fthiebolt/neOCampus-arduino/pcb/old-altium-pcb-v3/single-ic-preamp-by-lm358.pdf

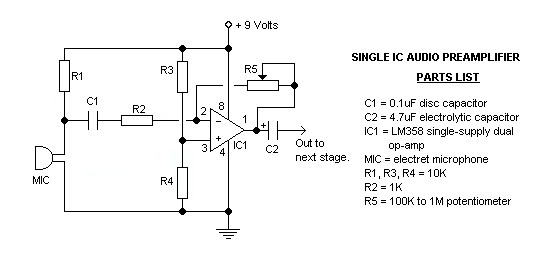
[picture p2: page 1]
