fthiebolt/neOCampus-arduino/pcb/old-altium-pcb-v3/sonometre2.pdf

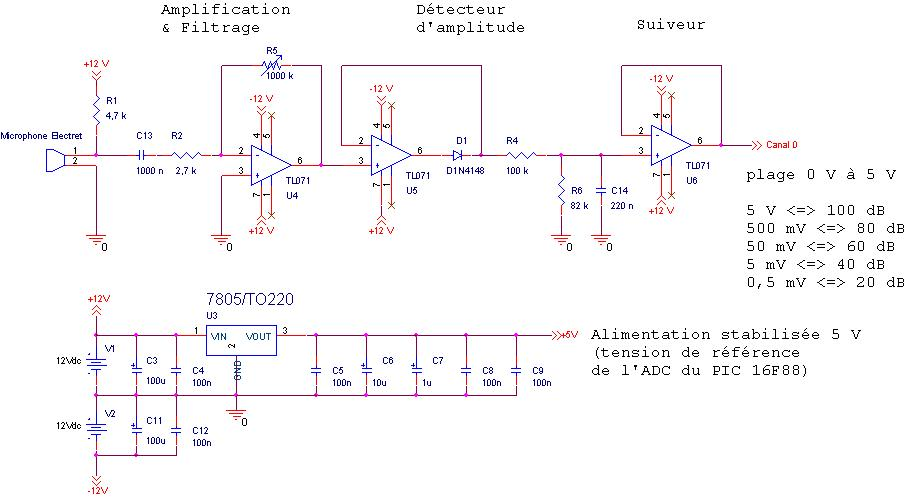
[picture p3: page 1]
