fthiebolt/neOCampus-arduino/pcb/old-altium-pcb-v3/TaaraESP-SHT21.sch_.pdf

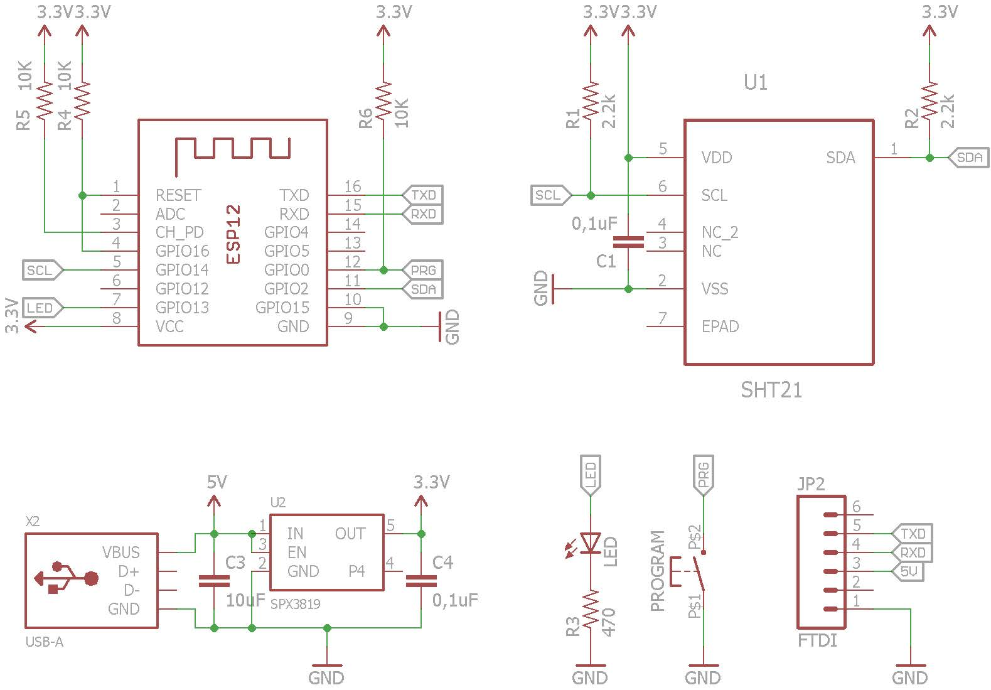
[picture p4: page 1]
