fthiebolt/neOCampus-arduino/lasercut/LaserCut-parameters_oct23.jpg

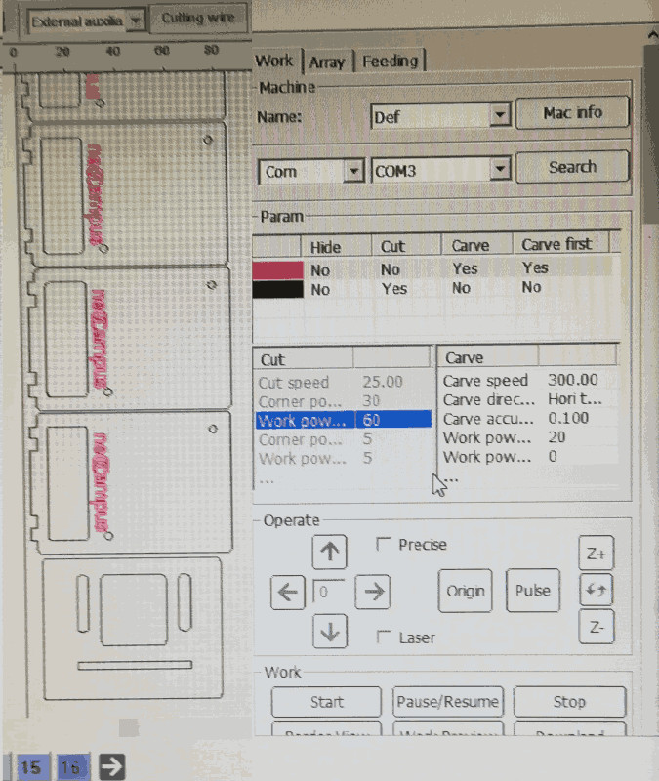
lasercut/LaserCut-parameters_oct23.jpg
