fthiebolt/neOCampus-arduino/pcb/pcb-v5/layout-outline.pdf

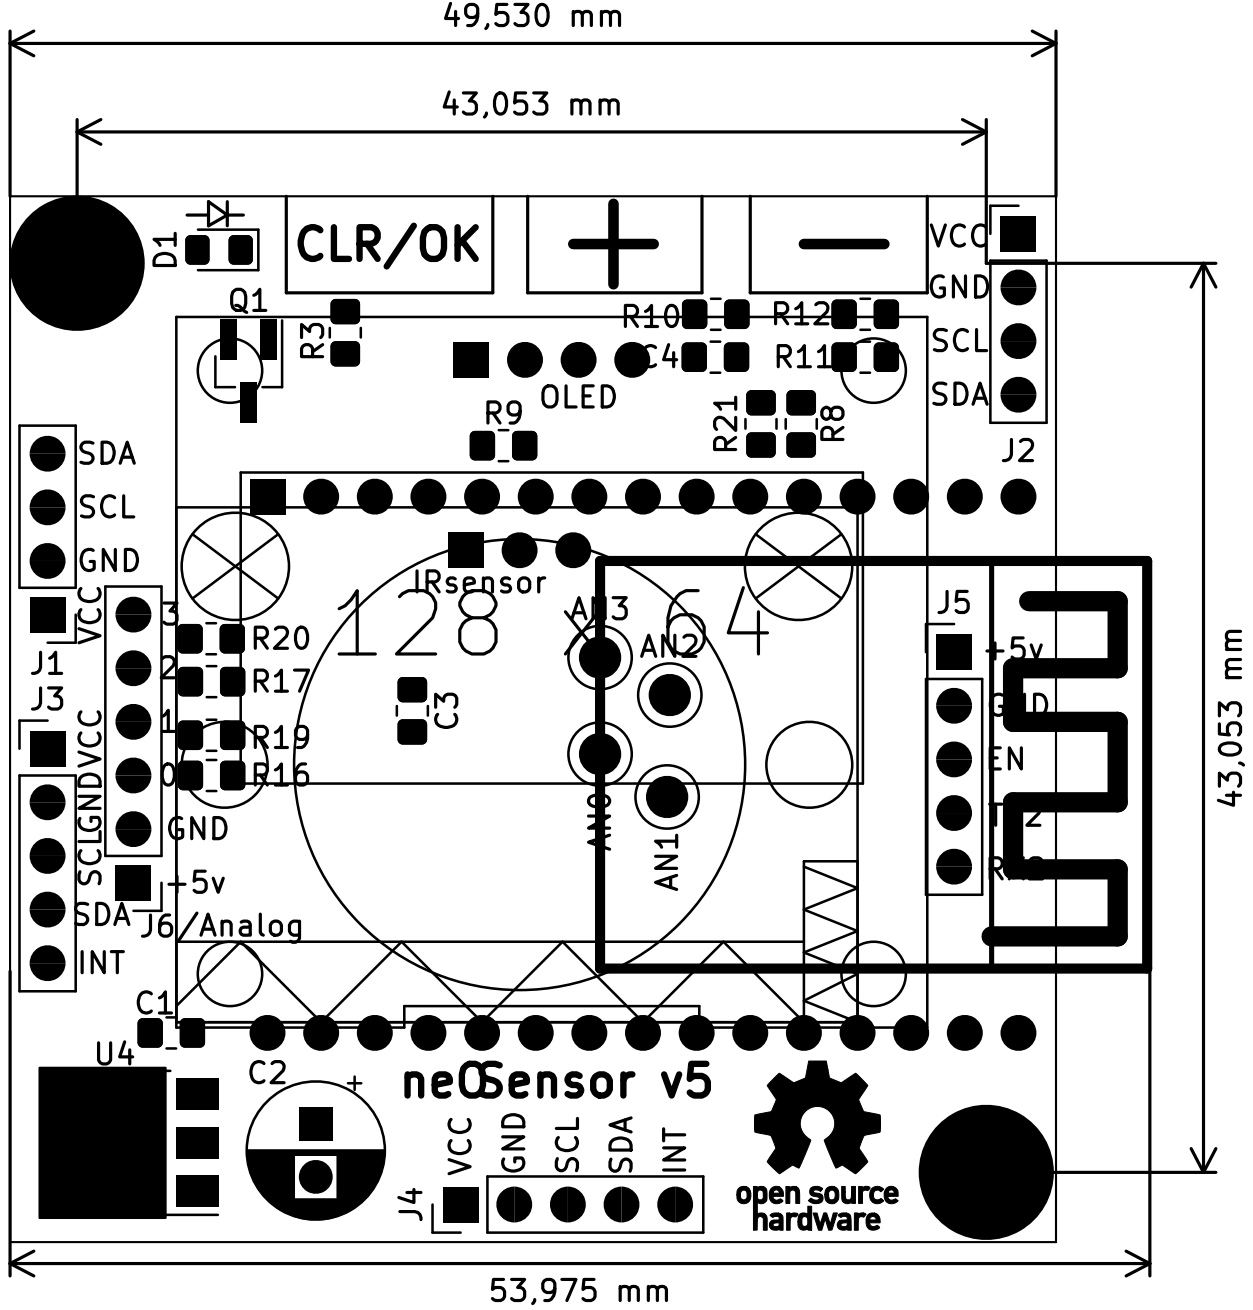
[picture p32: page 1]
