fthiebolt/neOCampus-arduino/pcb/old-altium-pcb-v3/Cpt_temperature.pdf

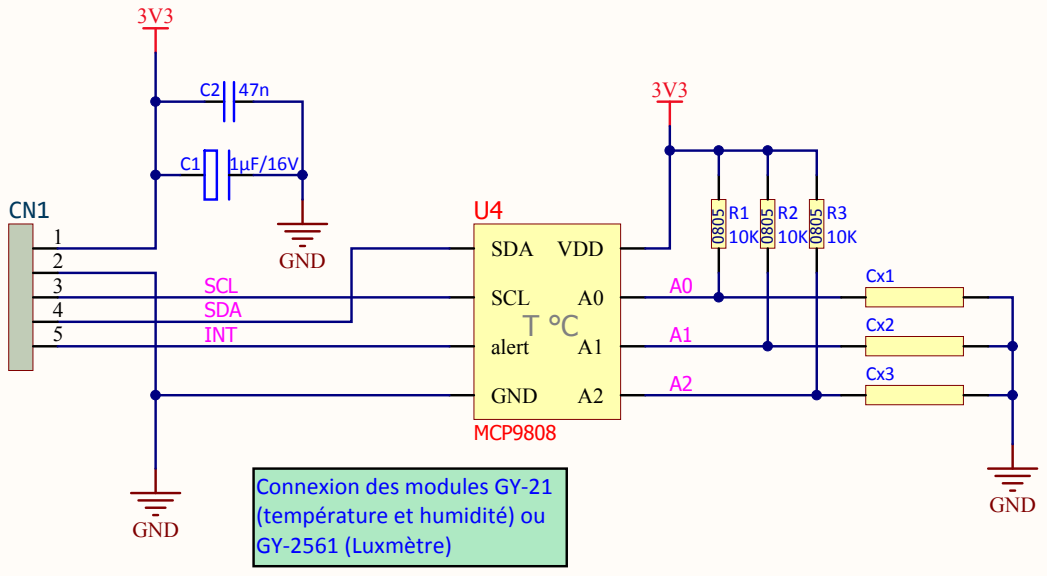
[picture p33: page 1]

GND

SDA | A1
INT

Connexion des modules GY-21
(température et humidité) ou
GY-2561 (Luxmètre)

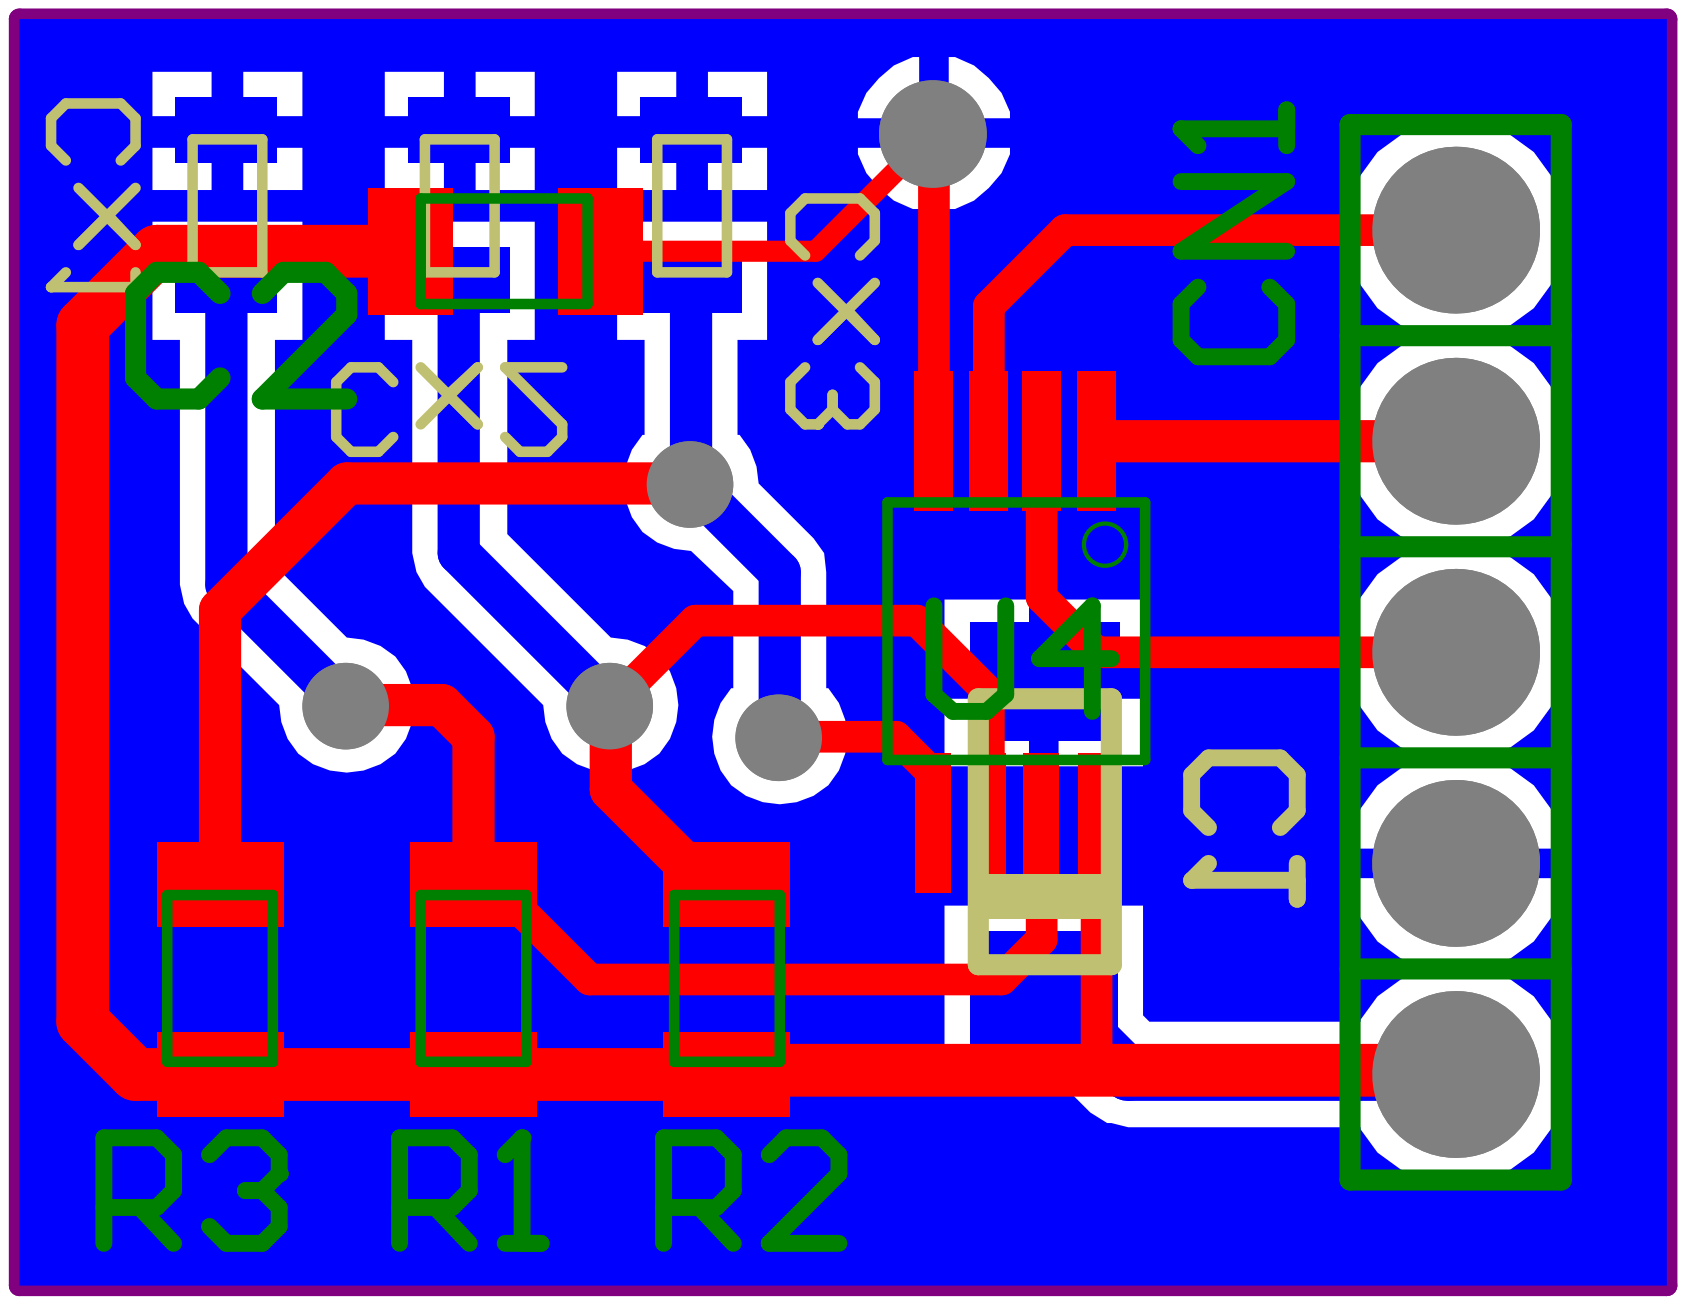
[picture p34: page 2]

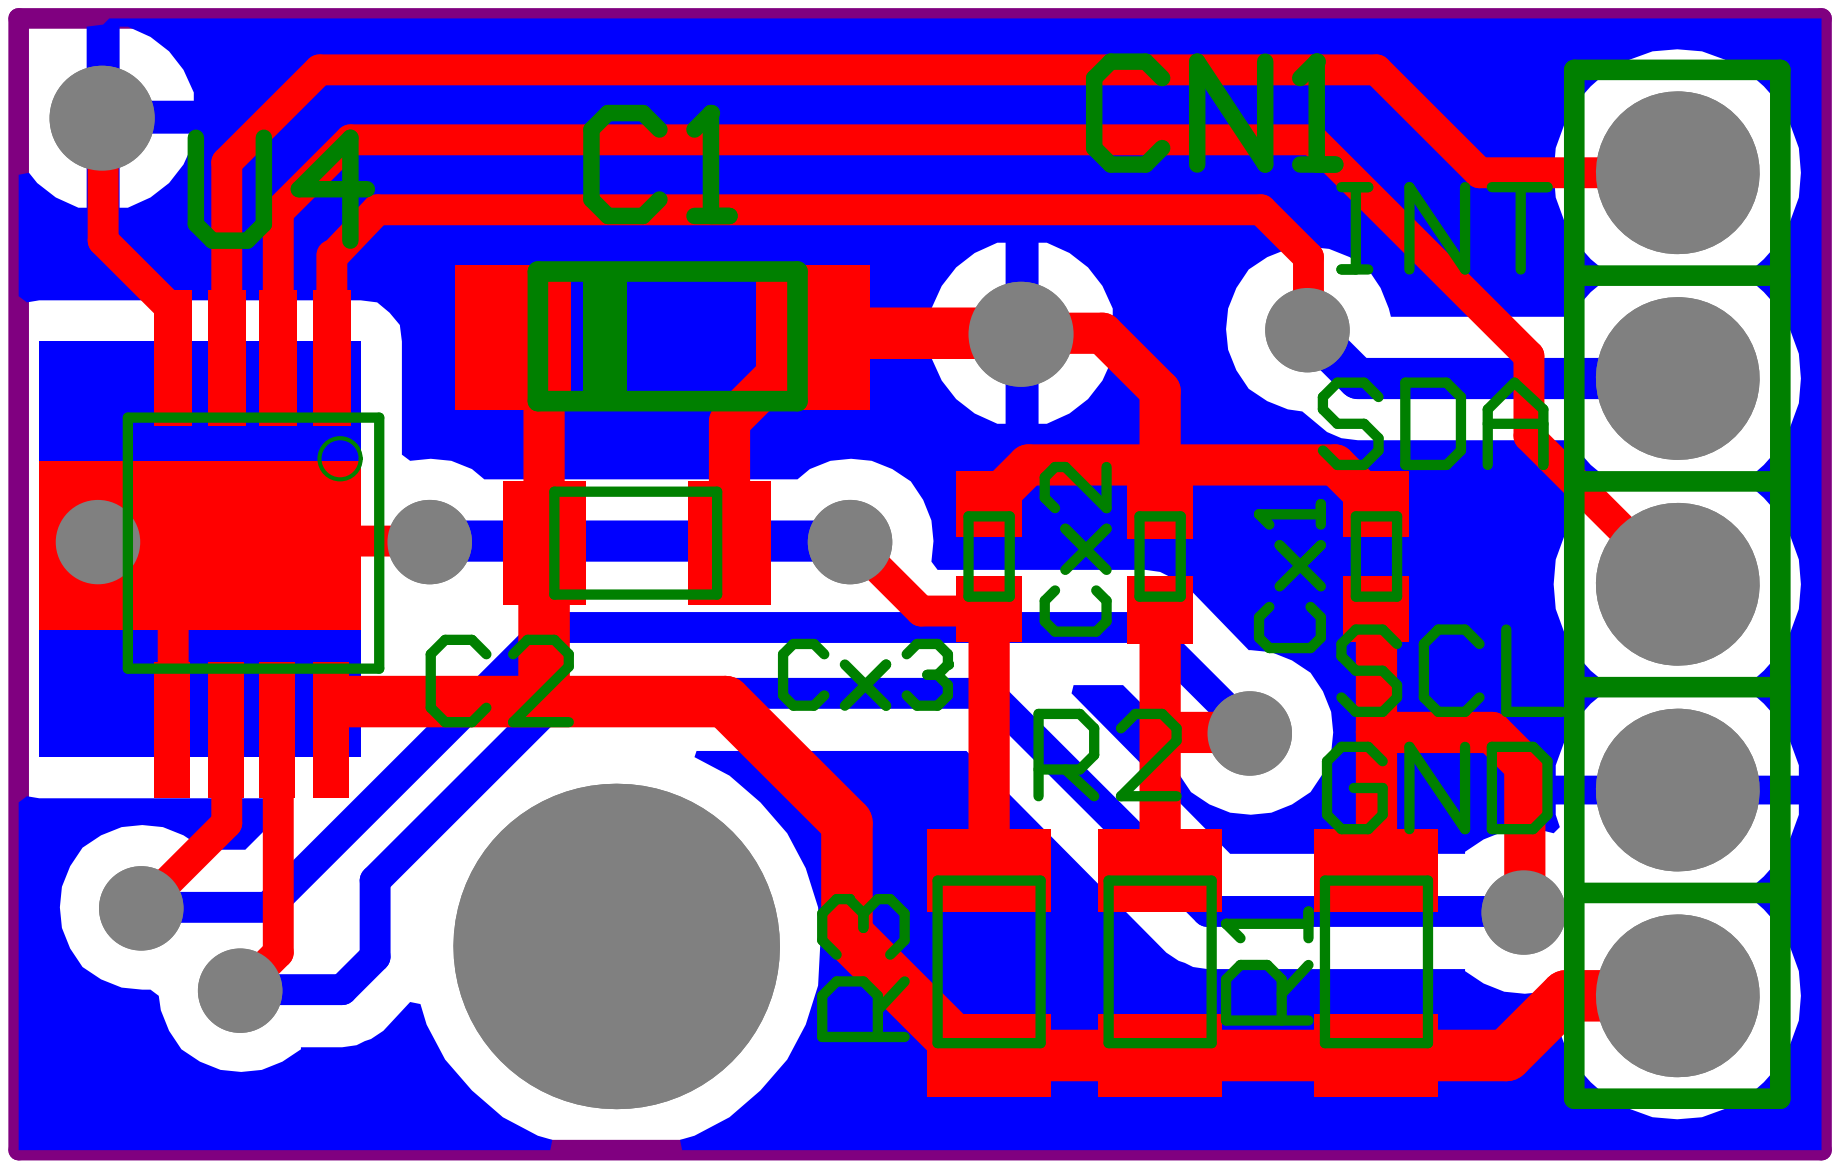
[picture p35: page 3]

Comment | Description | Designator | Footprint | LibRef | Quantity
1µF/ 16V | 145-7406 case 3216-18 | C1 | 3216-18 | tantale 1µF/ 16V | 1
47n | CMS 0805 | C2 | 0805 | Cap_CMS_0805 | 1
inch_ligne 1x5 | Inch_1x5_droit | CN1 | INCH_1x5_droit | Inch_1x5_droit | 1
Pont | Pont pour configuration I2C | Cx1, Cx2, Cx3 | 0402 | Pont | 3
10K | CMS 0805 | R1, R2, R3 | 0805 | Res CMS 0805 | 3
MCP9808 | Digital temperature SeU4 | | MSOP-08 | MCP9808 | 1
