fthiebolt/neOCampus-arduino/pcb/old-altium-pcb-v3/Son_BU.pdf

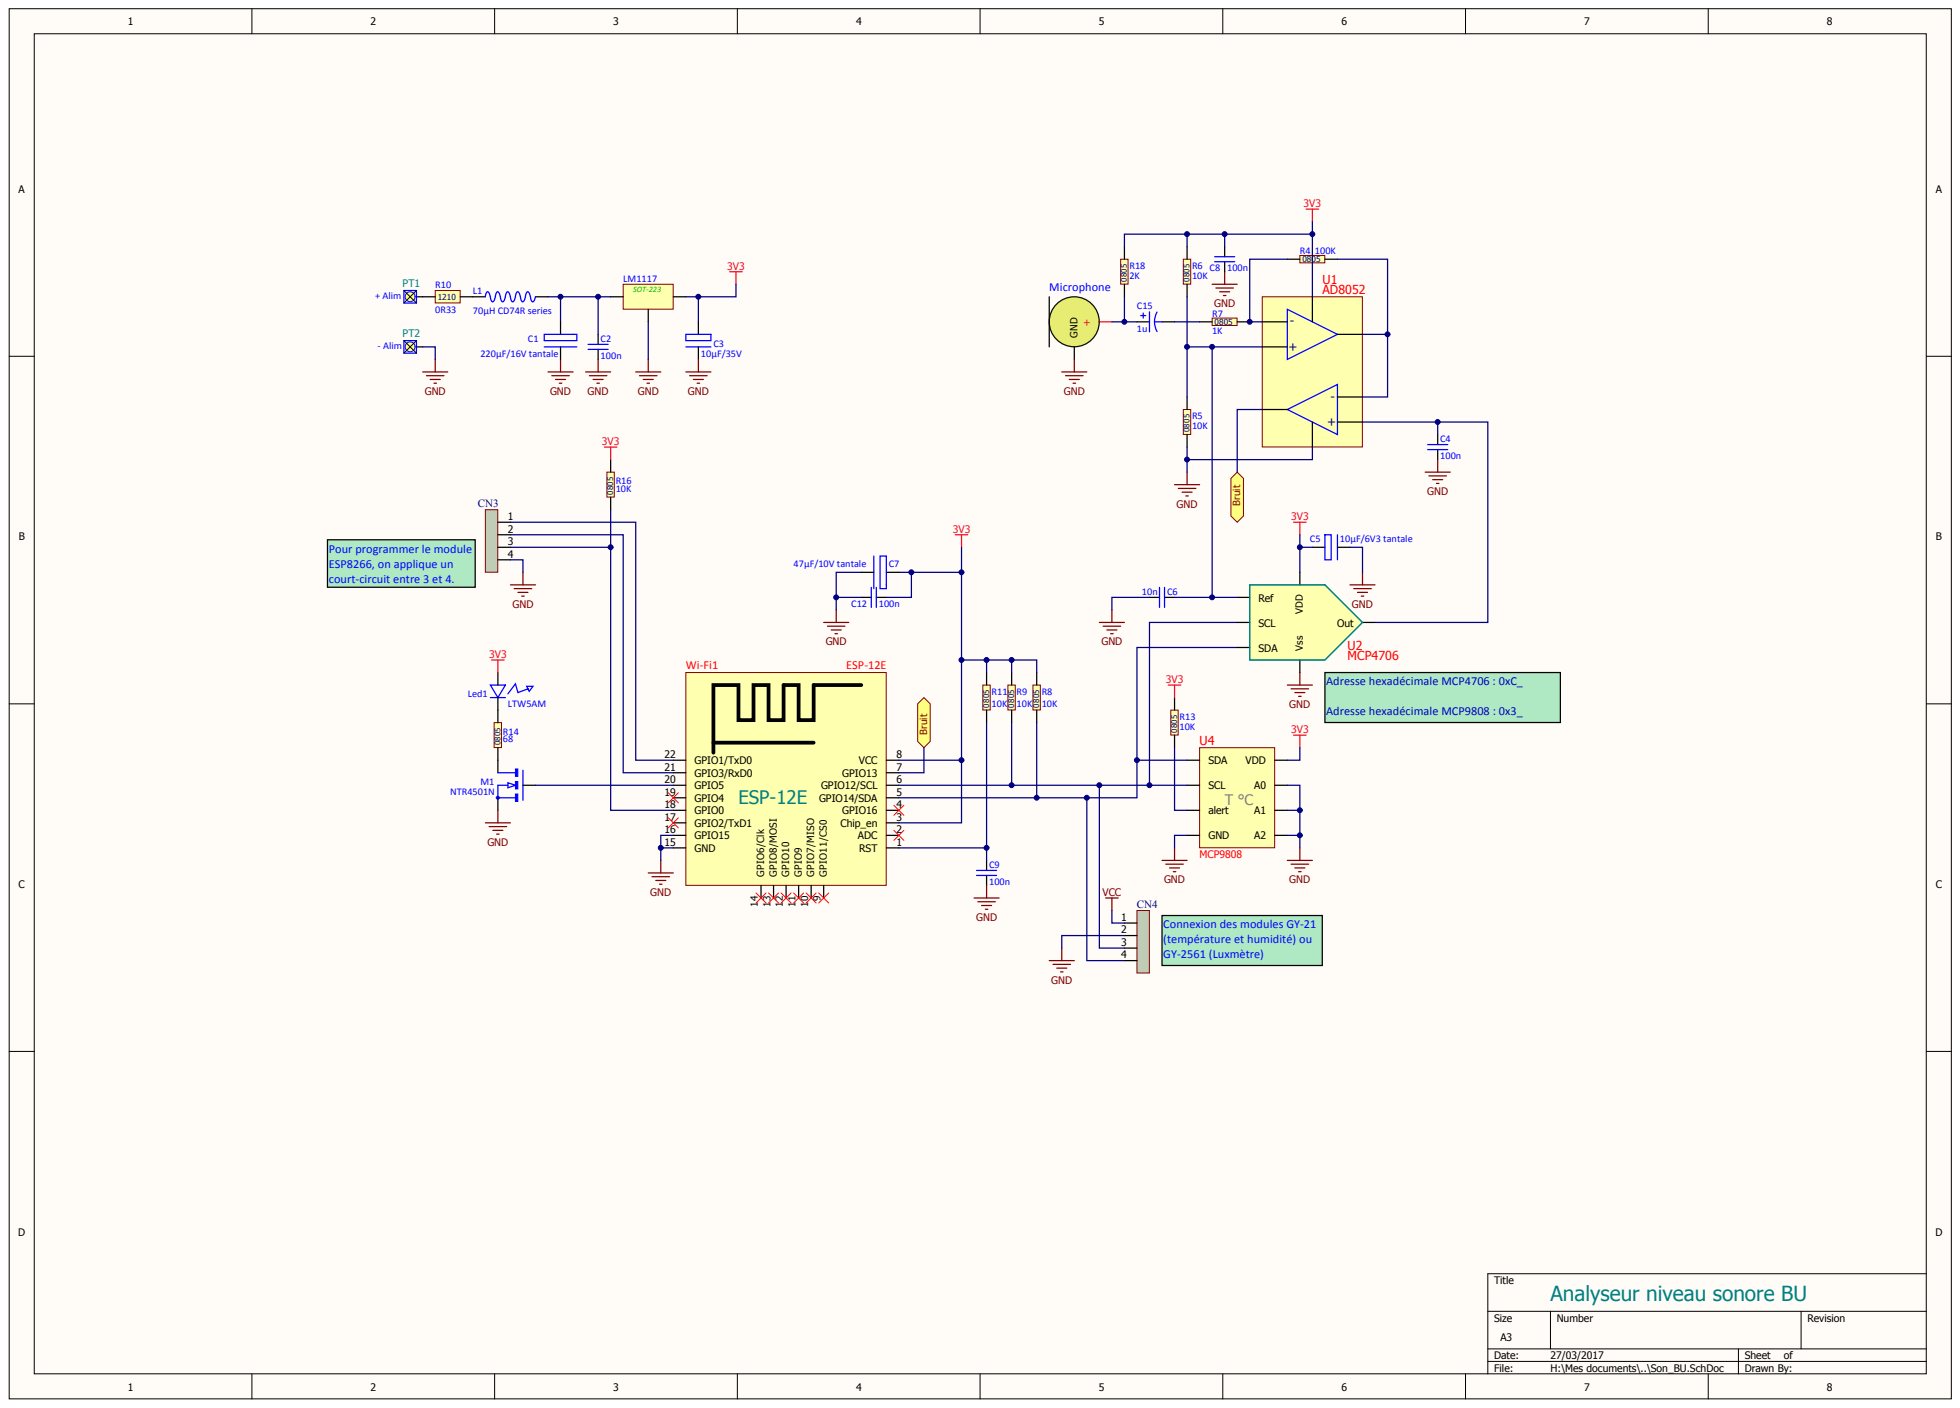
[picture p36: page 1]

Pour programmer le module
ESP8266, on applique un
court-circuit entre 3 et 4.

Connexion des modules GY-21
(température et humidité) ou
GY-2561 (Luxmètre)

Titl
Analyseur niveau sonore BU

Bill of Materials | <Parameter Title not found>
Source Data From: | Son_BU.PrjPCB
Project: | | Son_BU.PrjPCB
Variant: | | None
Creation Date: 27/03/2017 | 09:28:08
Print Date: | 42821 | 42821,39458
Footprint | Comment | LibRef | Designator | Description | Quantity
7343-31 | 220µF/16V
| tantale | tantale
| | 220µF/16V | C1 | 253-5290 | 1
0805 | 100n | Cap_CMS_0805 | C2, C4, C8, C9, C12 | CMS 0805 | 5
Condo CMS POL diam.5 | 10µF/35V | 10µF/35V | C3 | électrochimique CMS 185-0112 | 1
Tantale 10µF/6V3 | 10µF/6V3
| tantale | tantale
| | 10µF/6V3 | C5 | 175-4041 ou 145-7412 case 3216-18 | 1
0805 | 10n | Cap_CMS_0805 | C6 | CMS 0805 | 1
tantale 47µF/10V | 47µF/10V
| tantale | tantale
| | 47µF/10V | C7 | 175-4168 | 1
RB7.6-15 | Cap Pol1 | Cap Pol1 | C15 | Polarized Capacitor (Radial) | 1
INCH_1x4_dr oit | inch_ligne 1x4 | Inch_1x4_droit | CN3, CN4 | Inch_1x4_droit | 2
SELF CD74R | 70µH CD74R
| series | Self CD74R | L1 | SMT CD74R Aliexpress | 1
LTW5AM | LTW5AM | LTW5AM LED | Led1 | LED Golden Dragon Plus | 1
SOT-223 thermo1 | LM1117/33 | LM1117MPX-3.3 | LM1117 | Régulateur SOT-223 | 1
SOT23 (NTR4501) | NTR4501N | NTR4501N | M1 | MOSFET canal N | 1
Micro_electre t | Microphone_01 | Microphone_01 | Microphone | | 1
Pointe de test | + Alim | PTEST | PT1 | pointe de test CI 133-6225 | 1
Pointe de test | - Alim | PTEST | PT2 | pointe de test CI 133-6225 | 1
0805 | 100K | Res CMS 0805 | R4 | CMS 0805 | 1
0805 | 10K | Res CMS 0805 | R5, R6, R8, R9, R11, R13, R16 | CMS 0805 | 7
0805 | 1K | Res CMS 0805 | R7 | CMS 0805 | 1
1210 | 0R33 | Res CMS 1210
| | ERJ14B | R10 | CMS 1210 | 1
0805 | 68 | Res CMS 0805 | R14 | CMS 0805 | 1
0805 | 2K | Res CMS 0805 | R18 | CMS 0805 | 1
SOIC08 | AD8052 | AD8052 | U1 | AOP | 1
SOT23-6 | MCP4706 | MCP4706_1 | U2 | DAC I2C (RS : 738-7111) | 1
MSOP-08 | MCP9808 | MCP9808 | U4 | Digital temperature Sensor | 1
ESP-12E | ESP-12E | ESP-12E | Wi-Fi1 | ESP-12E module Wi-Fi | 1
| | | | | 36
Approved | | Notes
