fthiebolt/neOCampus-arduino/pcb/old-altium-pcb-v3/Assembly Drawings.pdf

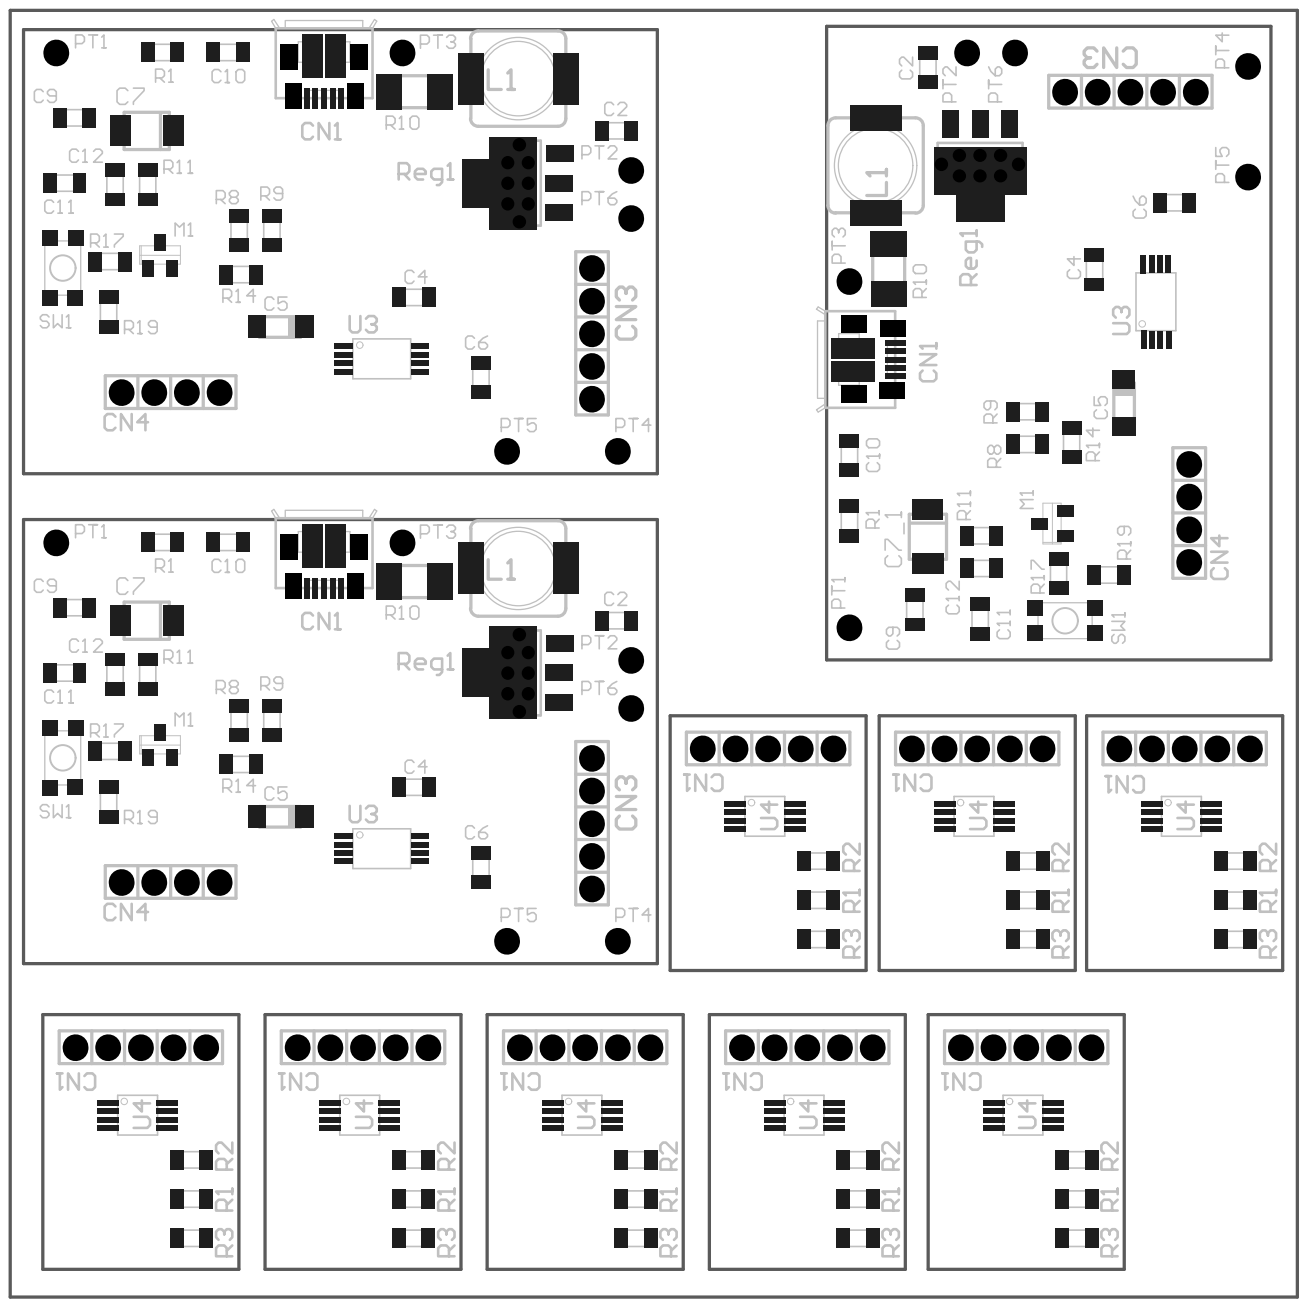
[picture p44: page 1]

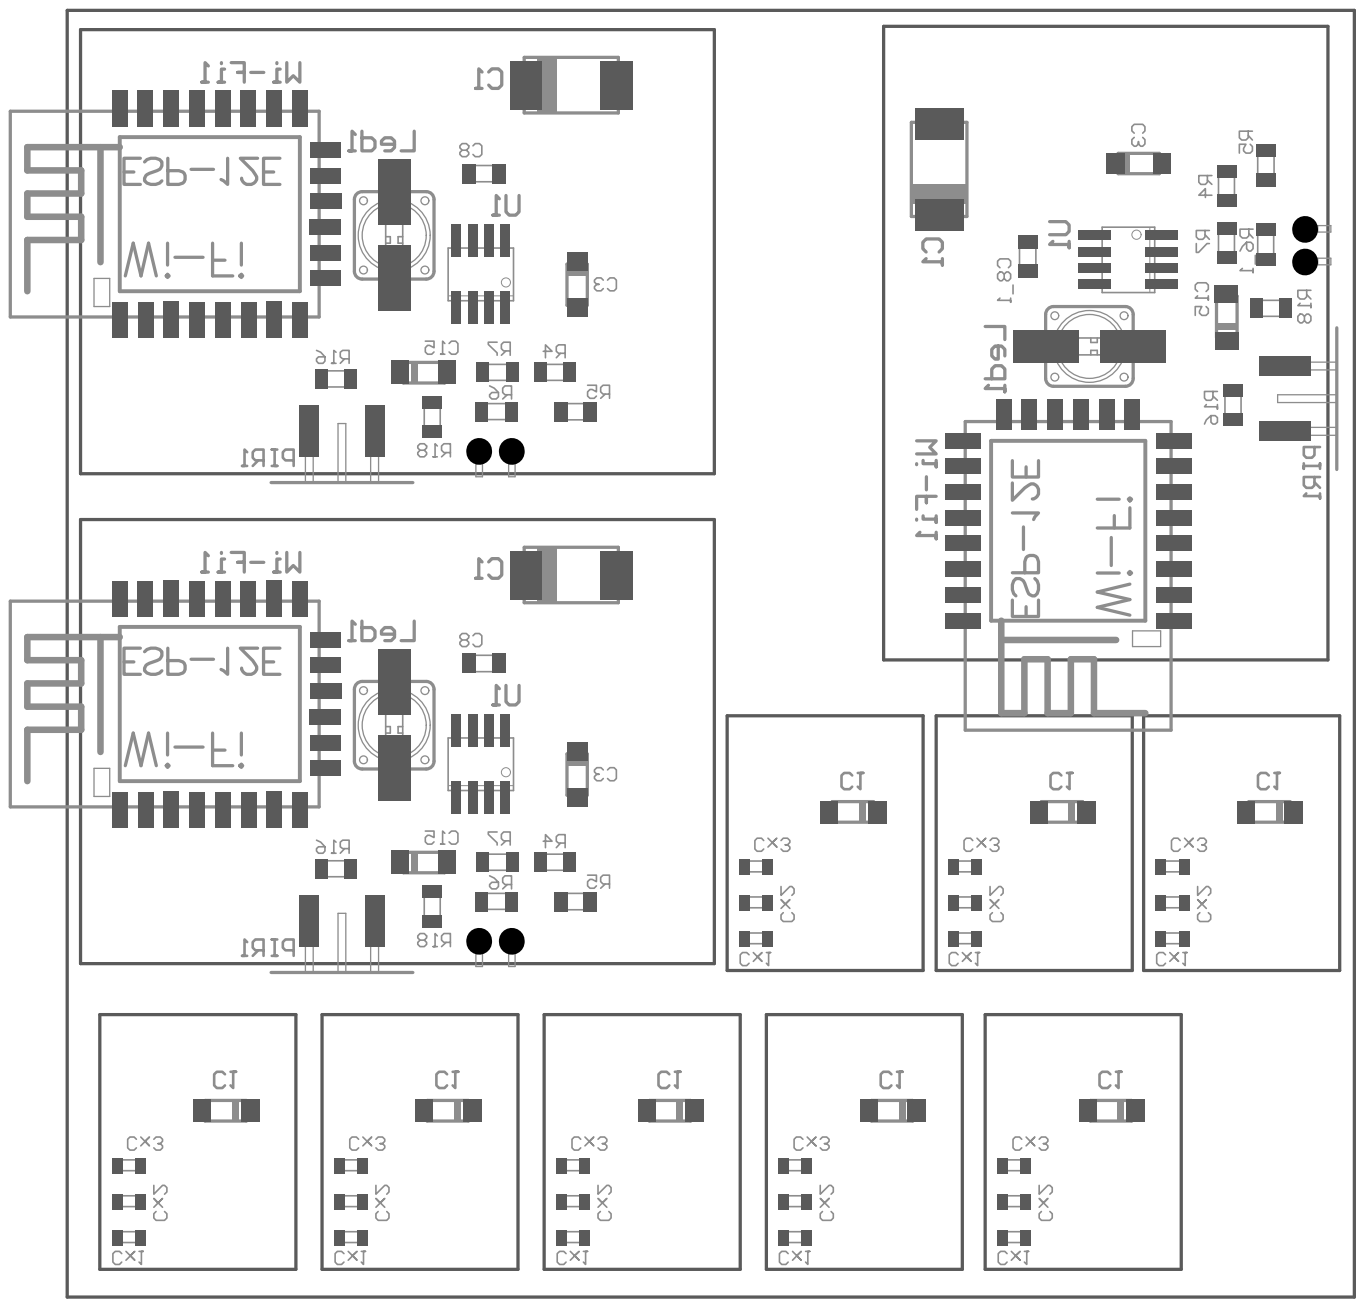
[picture p45: page 2]
