fthiebolt/neOCampus-arduino/pcb/pcb-v4/neOSensor-v4-schematic.pdf

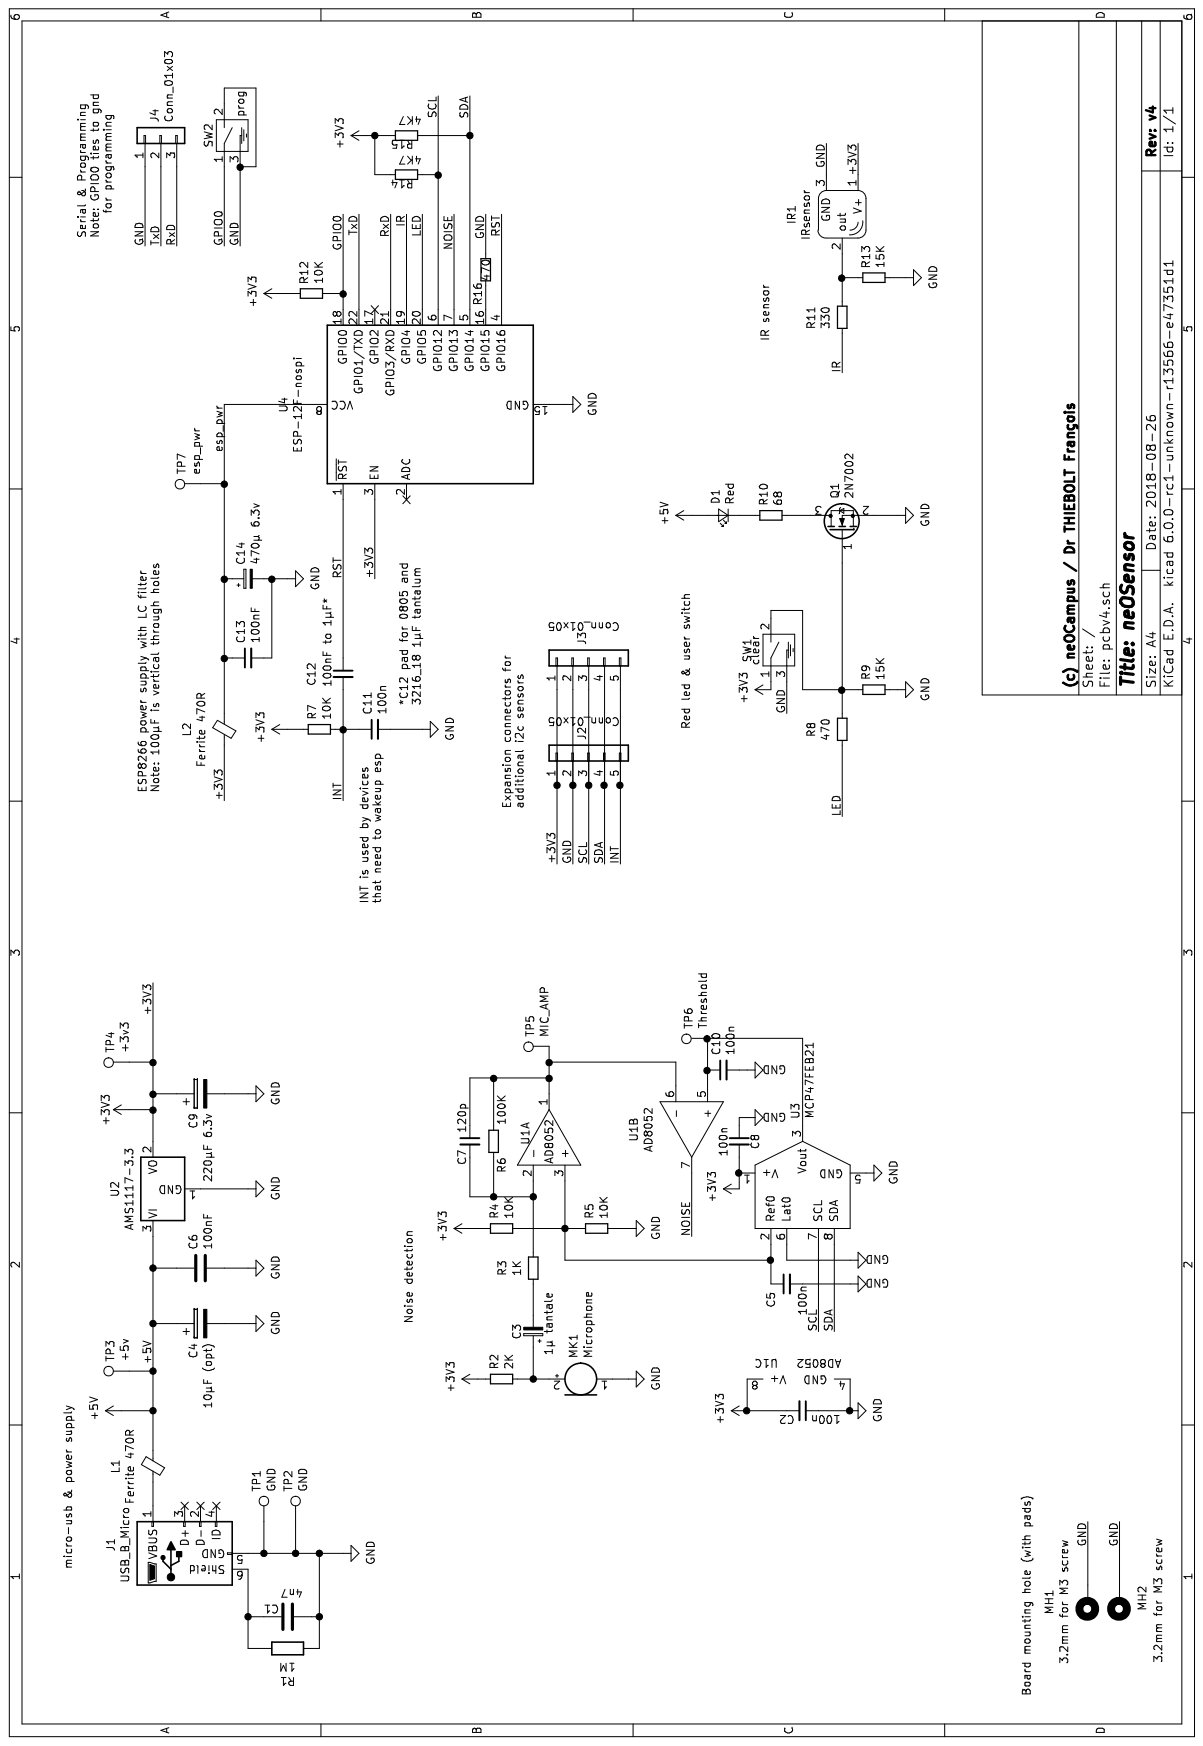
[picture p46: page 1]
