fthiebolt/neOCampus-arduino/pcb/old-altium-pcb-v3/Composite Drill Drawing.pdf

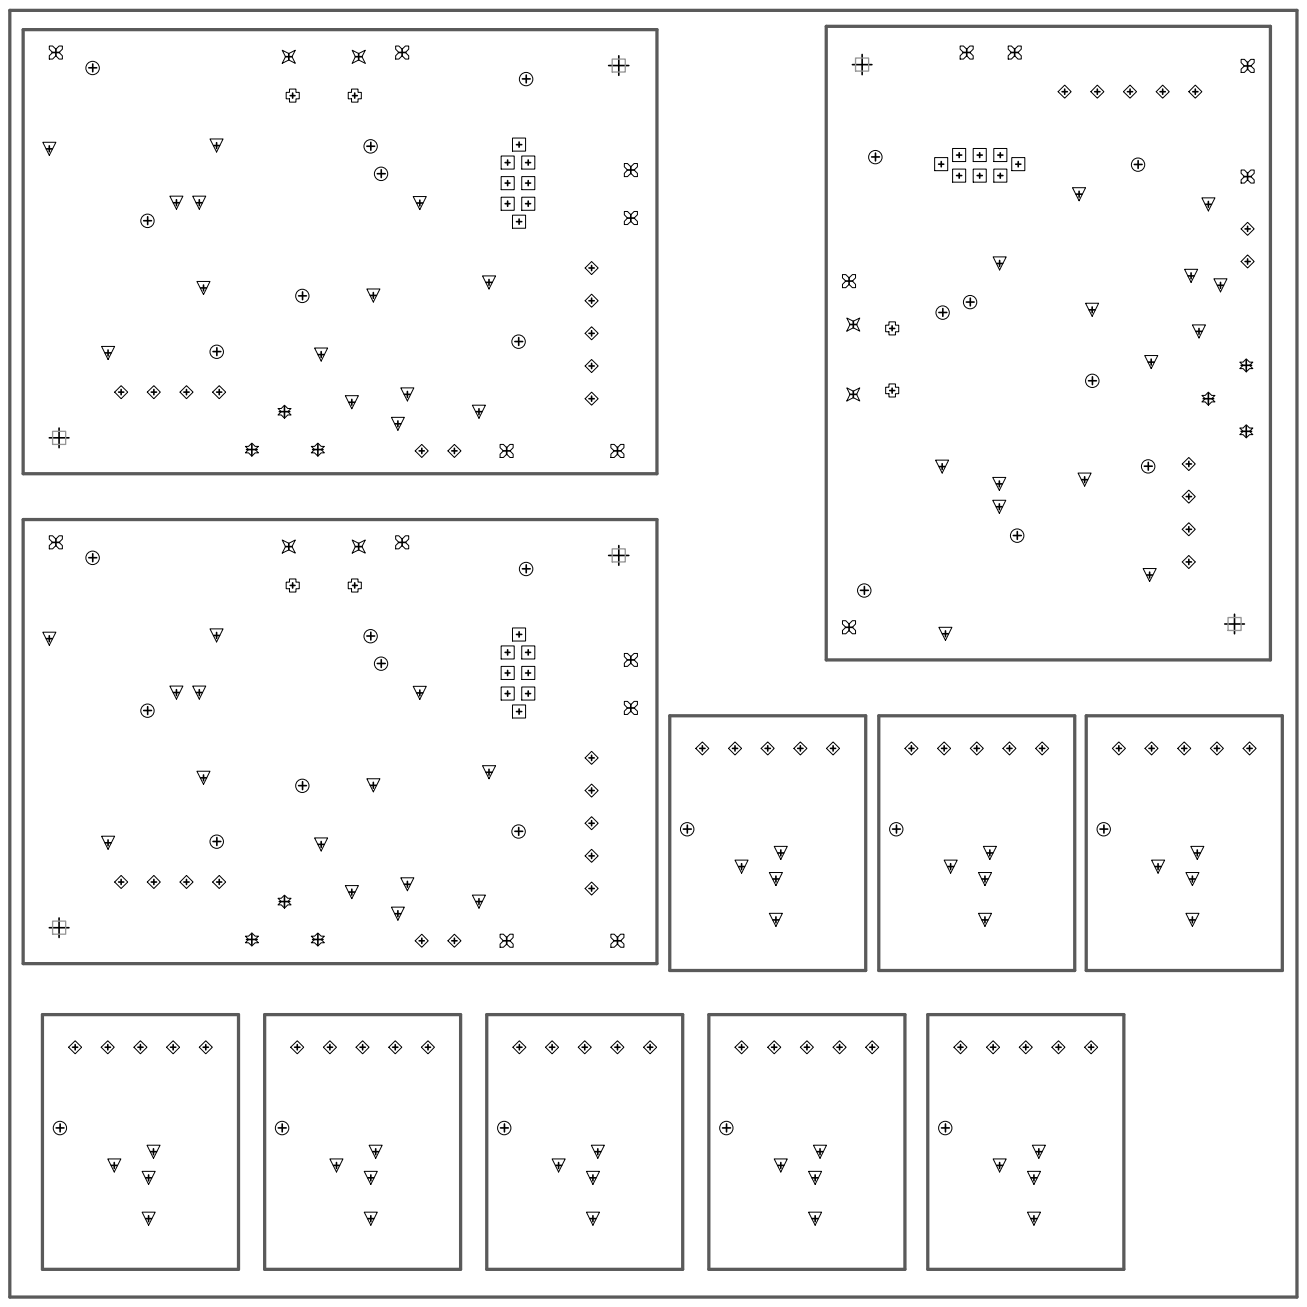
[picture p47: page 1]
