fthiebolt/neOCampus-arduino/pcb/pcb-v4/pcbv4-drilling4faces.pdf

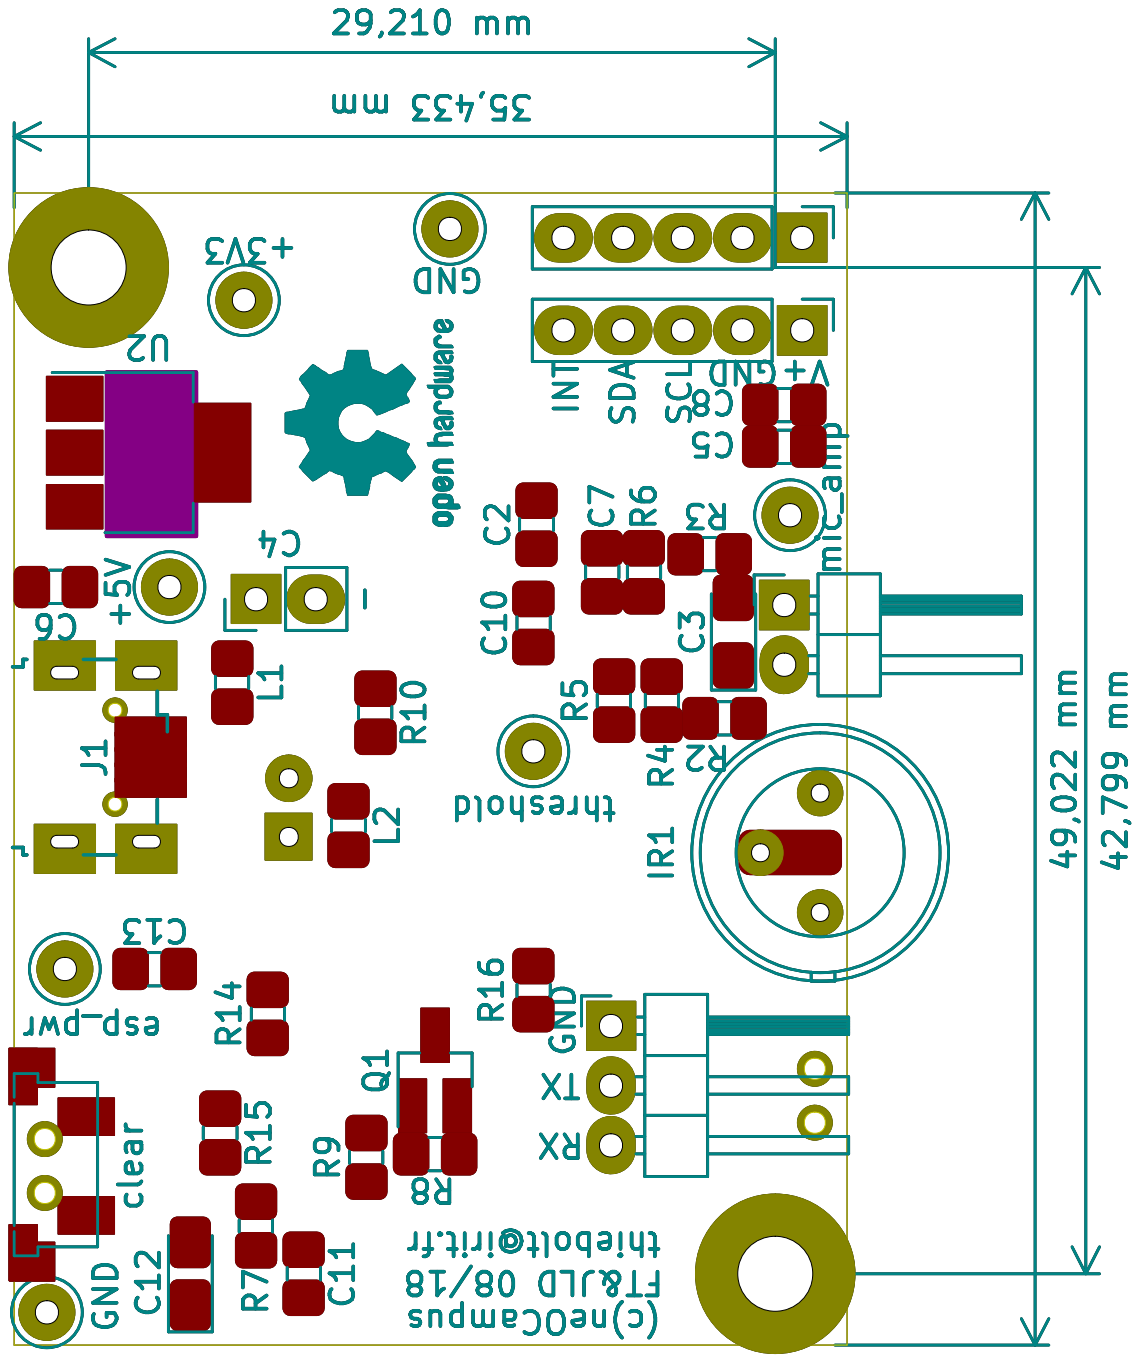
[picture p48: page 1]
