fthiebolt/neOCampus-arduino/src/neosensor/src/httpsclient.cpp

#include "httpsclient.hpp"

httpsclient::httpsclient () {};

StaticJsonDocument<CRED_JSON_SIZE> httpsclient::get_credentials(uint8_t *mac_addr){
    /* TODO 
     * Add certificate if unsecure connection successful
     */
    log_debug("--- beg of httpsclient::get_credentials ---");
    const char* root_ca = NULL;
    const char* _cacert = NULL;
    const char* _clicert = nullptr;
    const char* _clikey = nullptr;
    StaticJsonDocument<CRED_JSON_SIZE> cred_json;
    WiFiClientSecure *wcsClient = new WiFiClientSecure;
    wcsClient->setCACert(_cacert);
    wcsClient->setCertificate(_clicert);
    wcsClient->setPrivateKey(_clikey);

    snprintf(_url, sizeof(_url), "%s%s%02X:%02X:%02X:%02X:%02X:%02X", AUTH_SERVER, CRED_REQ, mac_addr[0],mac_addr[1],mac_addr[2],mac_addr[3],mac_addr[4],mac_addr[5]);
    //log_debug(_url);
    if(!_https.begin(*wcsClient, _url)){
        log_error("Beginning of https communication failed" );
    }else{
        log_debug("https communication established");
        int httpCode= _https.GET(); 
        log_debug(httpCode);
        String payload;
        if (httpCode > 0) { 
            //Check for the returning code
            payload = _https.getString();
        }
        /* Unboxing credentials from cred server */
        DeserializationError error = deserializeJson(cred_json, payload);
        Serial.println("Credentials requested from auth");
        log_debug(_url);
        _https.end();   
        // Test if parsing succeeds.
        if (error) {
            Serial.print(F("deserializeJson() failed: "));
            Serial.println(error.c_str());
        }else{
            log_debug("--- end of httpsclient::get_credentials ---");
        }
    }
    return cred_json;
}
