fthiebolt/neOCampus-arduino/src/neosensor/src/esp32_memory.hpp

#ifndef MEMORY_HPP
#define MEMORY_HPP

#include <Arduino.h>
#include <ArduinoJson.h>
#include <FS.h>
#include <LITTLEFS.h>
#include "const.hpp"
#include "neologger.hpp"

class esp32_memory{
public:
    /* starting the file system*/
    esp32_memory();
    bool begin(bool);


    void makedir(const char * path);

    void rmvdir(const char * path);

    /* checks if a file exists */
    bool exists(const char *);

    /* Writes a buffer int a file */
    void write(const char *, StaticJsonDocument<MAX_JSON_SIZE>);
    /* Read from a file
     * return what has been read.
     */
    StaticJsonDocument<MAX_JSON_SIZE> read(const char *);
};



#endif
