fthiebolt/neOCampus-arduino/src/neosensor/src/mqttsclient.hpp

#ifndef MQTTSCLIENT_HPP
#define MQTTSCLIENT_HPP

#include <Arduino.h>
#include <PubSubClient.h>
#include <WiFiClientSecure.h>
#include "const.hpp"
#include "neologger.hpp"


class mqttsclient{
public:
    /* Default constructor leads to the sandbox mode */
    mqttsclient(const char *login = DEFT_LOGIN, const char *pwd = DEFT_PWD, const char *server = DEFT_SERVER, unsigned int port = DEFT_PORT,const char *topic_base = DEFT_TOPIC_BASE, const char *topic = DEFT_TOPIC);
    /* destructor */
    ~mqttsclient();
    /* callback renamed to fit neOCampus logic */
    void on_message(char* topic, byte *payload, unsigned int length); //TODO
    /* subscribe to topic */
    bool subscribe(); //TODO
    /* publish */
    bool publish(); //TODO
    /* add a sensor class to the sensitivity list*/
    bool add(const char *, void(*)(byte *, unsigned int)); //TODO
    /* connection to the MQTT broker*/
    bool connect();
    /* reconnect if connection lost */
    void reconnect();
    /* print attributes to serial */
    void serialize();

    /* extracts the topic from the long string returned by the callback*/ 
    char * split_topic(char *topic_chain);
private:
    WiFiClientSecure *_wcsClient = new WiFiClientSecure;
    PubSubClient _client; 
    const char *_login; 
    const char *_pwd; 
    const char *_server;
    const char *_topic_base;
    const char *_topic;
    const unsigned int _port;
    struct users{
        const char* topic;
        size_t topic_size;
        void(*on_message)(byte*, unsigned int);
    } _users [MAX_SENSORS]; 
    int _numb_users;


};


#endif
