fthiebolt/neOCampus-arduino/tests/dual_MQTTS_subscription_test/dual_MQTTS_subscription_test.ino

#include <WiFiManager.h>
#include <HTTPClient.h>
#include <PubSubClient.h>
#include <ArduinoJson.h>
#include <SPIFFS.h>

#define CREDENTIALS "/cred.txt"
#define CONFIG "/conf.txt"

#define DEFT_LOGIN "test"
#define DEFT_PWD "test"
#define DEFT_SERVER "neocampus.univ-tlse3.fr"
#define DEFT_TOPIC "TestTopic/airquality"
#define DEFT_TOPIC_CLASS "TestTopic/airquality/command"
#define DEFT_SEC_TOPIC "TestTopic/temperature"
#define DEFT_SEC_TOPIC_CLASS "TestTopic/temperature/command"

#define DEFT_PORT 8883

/* MAC vars */
uint8_t macAddr[6];
char strMacAddr[32];

/*WiFiManager vars */
char ssid[20]; /*WM ssid defined by device's class + part of MAC address*/
const char* pwd = "password"; /* need 8 char pwd else autoConnect fails.*/
WiFiManager wm;

/*HTTPS vars*/
HTTPClient httpsClient;
const char* root_ca = NULL;
char url [90];
const char* config_server = "https://sensocampus.univ-tlse3.fr/device/config";

/* JSon Vars */
StaticJsonDocument<200> JSON_cred;
StaticJsonDocument<1000> JSON_conf;/*
const char* cred_login = JSON_cred["login"];
const char* cred_pwd = JSON_cred["password"];
const char*  cred_server = JSON_cred["server"];
int cred_port = JSON_cred["port"];*/


/* MQTTS vars */
const char* _cacert = NULL;
const char* _clicert = nullptr;
const char* _clikey = nullptr;
WiFiClientSecure *wcsClient = new WiFiClientSecure;
PubSubClient client(*wcsClient);

void get_MAC(){
  Serial.println();
  Serial.print("ESP BOARD MAC Address: ");
  WiFi.macAddress(macAddr);
  snprintf( strMacAddr, sizeof(strMacAddr), "%02X:%02X:%02X:%02X:%02X:%02X", macAddr[0],macAddr[1],macAddr[2],macAddr[3],macAddr[4],macAddr[5]);
  snprintf(ssid, sizeof(ssid),"%s%02X:%02X","airquality_",macAddr[4], macAddr[5]);
  Serial.println(strMacAddr);
  Serial.println(ssid);
  snprintf(url, sizeof(url), "%s%s","https://sensocampus.univ-tlse3.fr/device/credentials?mac=",strMacAddr);
  Serial.println(url);
  Serial.flush();
}

void set_WiFi(){
  wm.resetSettings();
  WiFi.mode(WIFI_STA);
  if(!wm.autoConnect(ssid,pwd))
    Serial.println("Conn Doomed");
  else{
    Serial.println("Conn est");
  }
}

void get_credentials(){
  Serial.println("getting credentials");
  httpsClient.begin(url,root_ca);
    int httpCode = httpsClient.GET();
    if (httpCode > 0) { //Check for the returning code
      String payload = httpsClient.getString();
      Serial.println(httpCode);
      Serial.println(payload);
      /* Unboxing credentials from cred server */
      DeserializationError error = deserializeJson(JSON_cred, payload);
      Serial.println("Credentials requested from auth");
      // Test if parsing succeeds.
      if (error) {
        Serial.print(F("deserializeJson() failed: "));
        Serial.println(error.c_str());
        return;
      }
      
      /* Saving credentials to SPIFFS */
      File file = SPIFFS.open(CREDENTIALS, "w");
      if (!file) {
        Serial.println("Error opening file for writing");
        return;
      }
      if (serializeJson(JSON_cred, file) == 0) {
        Serial.println(F("Failed to write to file"));
      } else {
        Serial.println(F("Credentials successfully saved"));
      }
      file.close();
    }else {
      Serial.println(F("Error on HTTPs request"));
    }
    httpsClient.end();
}

void get_conf(){
  Serial.println("Attempting to get conf");
  const char* cred_login = JSON_cred["login"];
  const char* cred_pwd = JSON_cred["password"];
  const char*  conf_server = JSON_cred["server"];
  int conf_port = JSON_cred["port"];
  httpsClient.begin(config_server, root_ca );
  httpsClient.setAuthorization(cred_login, cred_pwd);
  int httpCode = httpsClient.GET();
   if (httpCode > 0) { //Check for the returning code
     String payload = httpsClient.getString();
     Serial.println(httpCode);
     //Serial.println(payload);
     /* Unboxing credentials from cred server */
     DeserializationError error = deserializeJson(JSON_conf, payload);
     // Test if parsing succeeds.
     if (error) {
       Serial.print(F("deserializeJson() failed: "));
       Serial.println(error.c_str());
       return;
     }
     serializeJsonPretty(JSON_conf,Serial);
     File file = SPIFFS.open(CONFIG, "w");
      if (!file) {
        Serial.println("Error opening file for writing");
        return;
      }
      if (serializeJson(JSON_conf, file) == 0) {
        Serial.println(F("Failed to write to config.txt"));
      } else {
        Serial.println(F("Config successfully saved"));
      }
      file.close();
   } 
   httpsClient.end();
}
void callback(char* topic, byte* payload, unsigned int length){
    byte* p = (byte*)malloc(length);
    memcpy(p, payload,length);
    char* arr = (char *)p;
    Serial.print("Message arrived [");
    Serial.print(topic);
    Serial.print("] ");
    if(strncmp(topic,DEFT_TOPIC_CLASS,size_t(sizeof(DEFT_TOPIC_CLASS)))==0){
        Serial.print(F(": airquality sensor has received this"));
        for (int i=0;i<length;i++) {
        Serial.print((char)payload[i]);
        }
        client.publish(DEFT_TOPIC,p,length);
    }
    if(strncmp(topic,DEFT_SEC_TOPIC_CLASS,size_t(sizeof(DEFT_SEC_TOPIC_CLASS)))==0){
        Serial.print(F(": temperature sensor has received this"));
        for (int i=0;i<length;i++) {
        Serial.print((char)payload[i]);
        }
        client.publish(DEFT_SEC_TOPIC, p,length);
    }
    Serial.println("");
}

void mqtts(){
wcsClient->setCACert(_cacert);
wcsClient->setCertificate(_clicert);
wcsClient->setPrivateKey(_clikey);
  Serial.println("Attempting to get conf");
  if(wcsClient) {
    const char* cred_login = JSON_cred["login"];
    const char* cred_pwd = JSON_cred["password"];
    const char*  conf_server = JSON_cred["server"];
    int conf_port = JSON_cred["port"]; 
    //client.setServer(conf_server, conf_port);
    client.setServer(DEFT_SERVER, DEFT_PORT);
    //if(client.connect(conf_server,cred_login, cred_pwd)){
      if(client.connect(DEFT_SERVER, DEFT_LOGIN, DEFT_PWD)){
      Serial.println(F("Client connected"));
      if(!client.subscribe(DEFT_TOPIC_CLASS)){
        Serial.print("Failed to subscribe to ");
        Serial.println(DEFT_TOPIC_CLASS);
      }else{
        Serial.print("subscribing done to ");
        Serial.println(DEFT_TOPIC_CLASS);
      }
      if(!client.subscribe(DEFT_SEC_TOPIC_CLASS)){
        Serial.print("Failed to subscribe to ");
        Serial.println(DEFT_SEC_TOPIC_CLASS);
      }else{
        Serial.print("subscribing done to ");
        Serial.println(DEFT_SEC_TOPIC_CLASS);
      }
      client.setCallback(callback);
    }else
      Serial.println(F("MQTT connection failed."));
  }else{
    Serial.println("Failed to set up WiFiClientSecure");
  }
}

void reconnect(){
  while(!client.connected()){
    Serial.print(F("MQTT connection pending..."));
    if(client.connect(DEFT_SERVER)){
      Serial.println(F("Connected"));
      client.subscribe(DEFT_TOPIC_CLASS);
      client.subscribe(DEFT_SEC_TOPIC_CLASS);
    }else{
      Serial.print("failed, rc=");
      Serial.print(client.state());
      Serial.println(" try again in 5 seconds");
      // Wait 5 seconds before retrying
      delay(5000);
    }
  }
}

void setup() {
  delay(3000);
  // put your setup code here, to run once:
  Serial.begin(115200);
  Serial.println(F("Hello ..."));
  delay(1000);
  bool success = SPIFFS.begin();
 
  if (success) {
    Serial.println("File system mounted with success");
  } else {
    Serial.println("Error mounting the file system");
    return;
  }
  get_MAC();
  set_WiFi();
  /* Do I have my credentials? */
  if(!SPIFFS.exists(CREDENTIALS))
    get_credentials();
  else{
  /* Yes i do */
    File file = SPIFFS.open(CREDENTIALS);
    if(!file){
      Serial.println("Failed to open file for reading");
      return;
    }
  /* credentials are stored as StaticJsonDocument, let's deserialize it*/
    DeserializationError error = deserializeJson(JSON_cred, file);
  // Test if parsing succeeds.
    if (error) {
      Serial.print(F("deserializeJson() failed: "));
      Serial.println(error.c_str());
      return;
    }
    file.close();
    Serial.println("Internal credentials found");
  } 
  Serial.println("I Have those credentials: ");
  serializeJsonPretty(JSON_cred,Serial);
  if(!SPIFFS.exists(CONFIG))
    get_conf(); 
  else{
  /* Yes i do */
    File file = SPIFFS.open(CONFIG);
    if(!file){
      Serial.println("Failed to open config for reading");
      return;
    }
  /* config is stored as StaticJsonDocument, let's deserialize it*/
    DeserializationError error = deserializeJson(JSON_conf, file);
  // Test if parsing succeeds.
    if (error) {
      Serial.print(F("deserializeJson() failed: "));
      Serial.println(error.c_str());
      return;
    }
    file.close();
    Serial.println("Internal config found");
    serializeJsonPretty(JSON_conf,Serial);
  }
  mqtts();
}

void loop() {
  // put your main code here, to run repeatedly:
  delay(1000);
  Serial.print(".");
  Serial.flush();
  if(!client.connected()){
    Serial.println(F("Connection lost, reconnecting... "));
    reconnect();
  }
  client.loop();
}
